ezrec/3dp-wilbur/stl/wilbur_fan_e3d_v6.stl

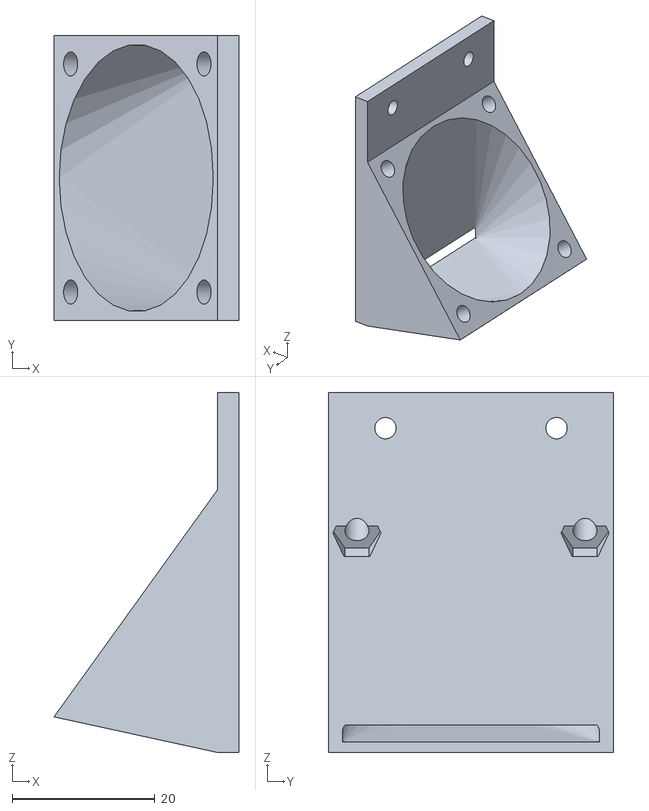
[picture p16: CAD file, 2019-10-02]
stl/wilbur_fan_e3d_v6.stl
25.9 x 40.0 x 50.5
