ezrec/3dp-wilbur/stl/wilbur_z_foot.stl

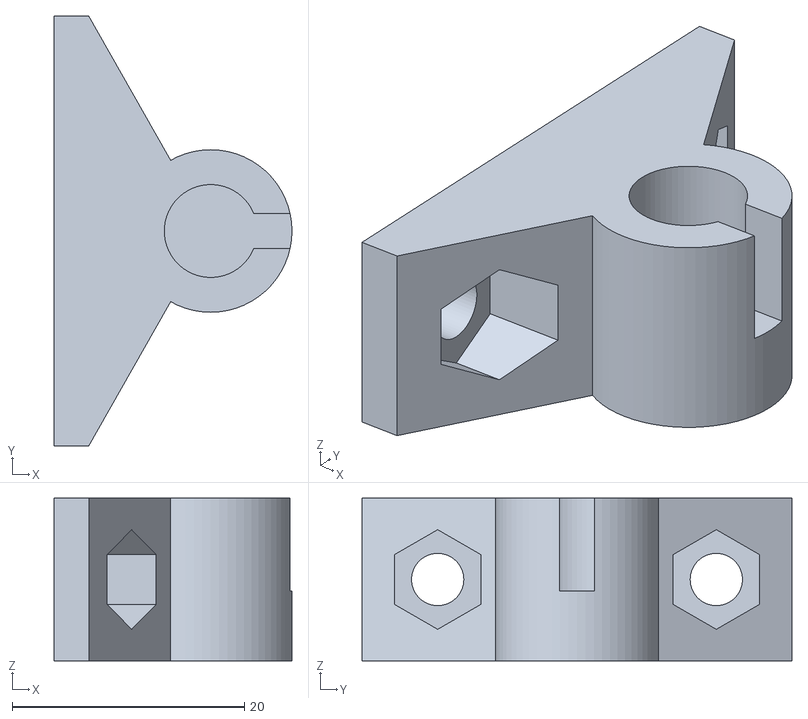
[picture p17: CAD file, 2019-10-02]
stl/wilbur_z_foot.stl
20.5 x 37.0 x 14.0
