ezrec/3dp-wilbur/stl/wilbur_y_motor_min.stl

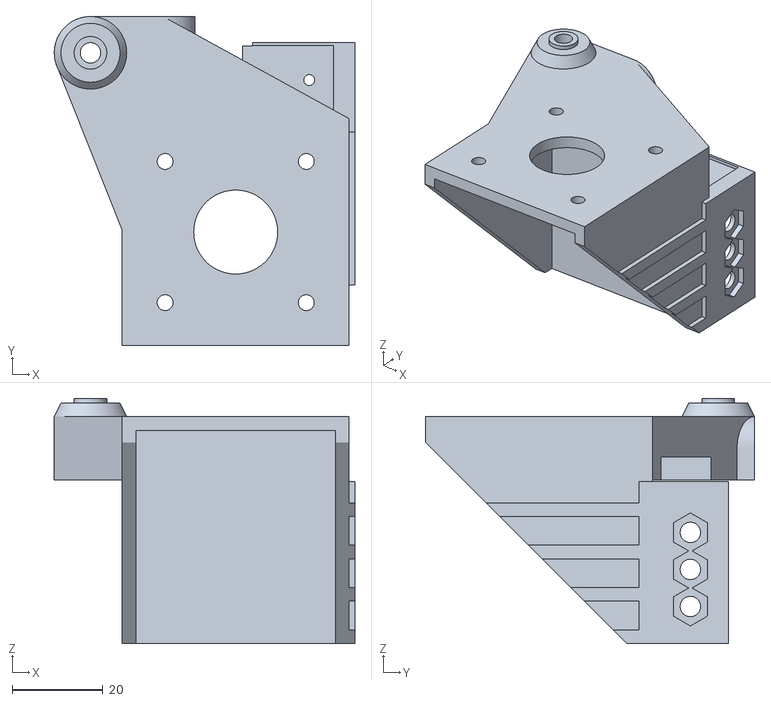
[picture p18: CAD file, 2019-10-02]
stl/wilbur_y_motor_min.stl
66.2 x 72.5 x 54.0
