ezrec/3dp-wilbur/stl/wilbur_power_box.stl

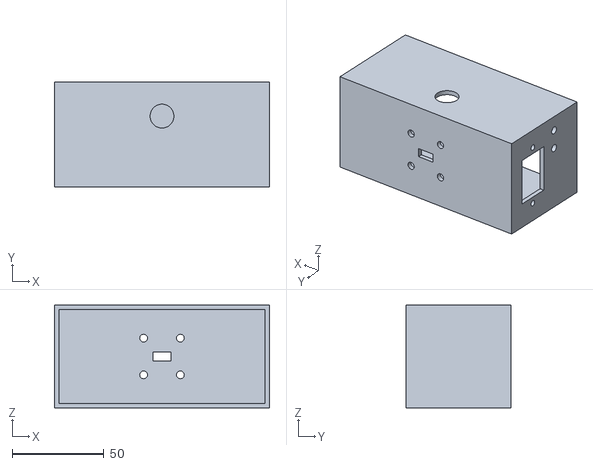
[picture p19: CAD file, 2019-10-02]
stl/wilbur_power_box.stl
117.0 x 57.0 x 56.0
