ezrec/3dp-wilbur/stl/wilbur_z_center.stl

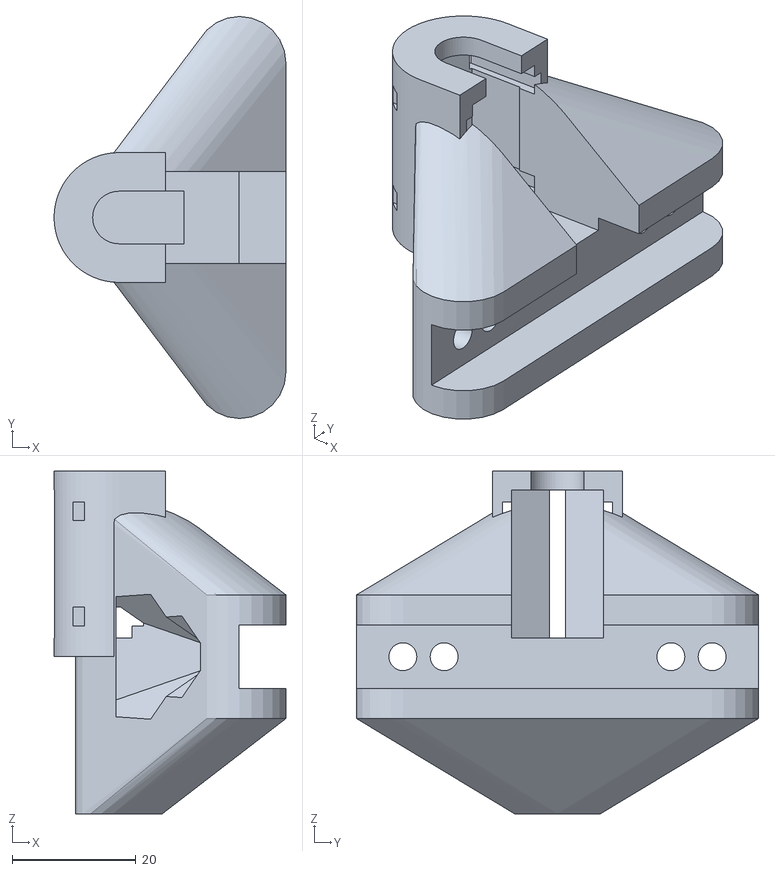
[picture p20: CAD file, 2019-10-02]
stl/wilbur_z_center.stl
37.5 x 65.0 x 55.4
