ezrec/3dp-wilbur/stl/wilbur_sensor_e3d_v6.stl

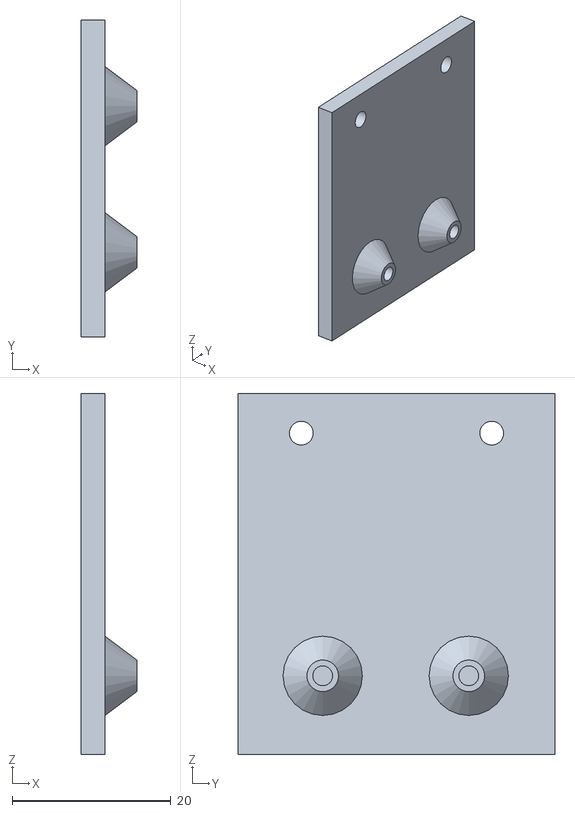
[picture p21: CAD file, 2019-10-02]
stl/wilbur_sensor_e3d_v6.stl
7.00 x 40.0 x 45.5
