ezrec/3dp-wilbur/stl/wilbur_sled.stl

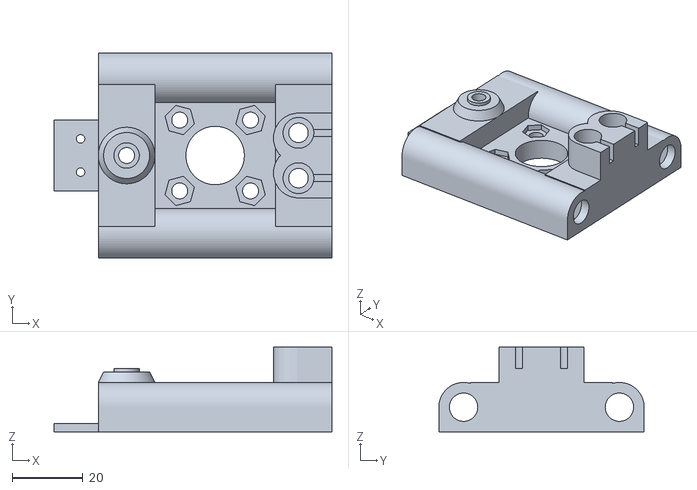
[picture p22: CAD file, 2019-10-02]
stl/wilbur_sled.stl
78.5 x 58.0 x 24.0
